michael1308/PogoProbe/assembly/20230415_011109.jpg

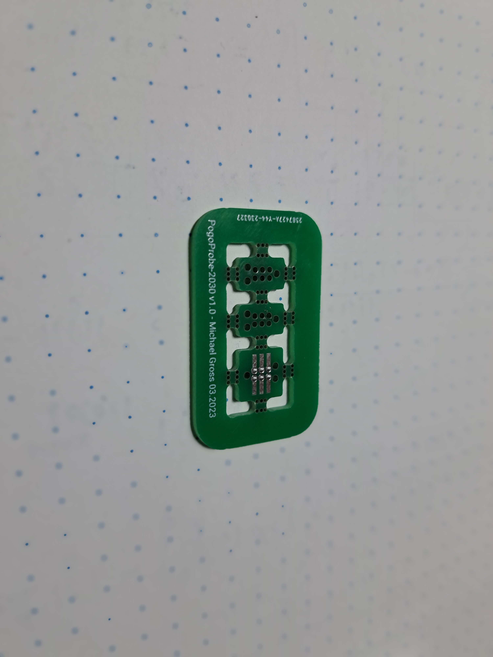
assembly/20230415_011109.jpg
