michael1308/PogoProbe/assembly/20230415_012053.jpg

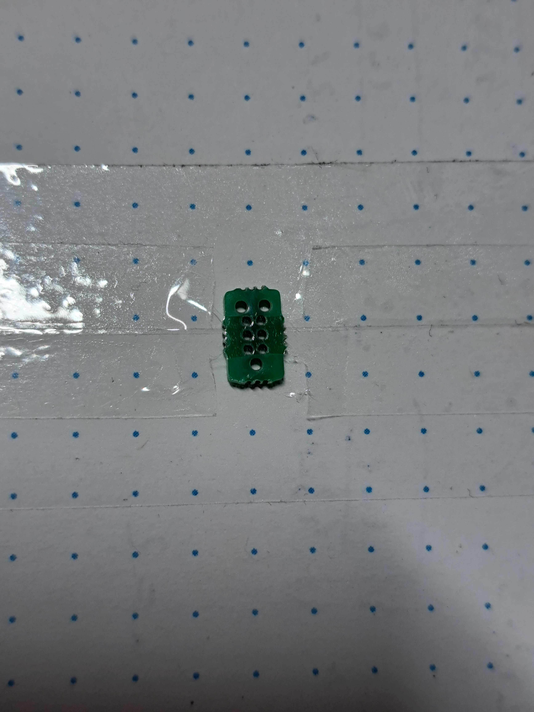
assembly/20230415_012053.jpg
