michael1308/PogoProbe/assembly/20230415_012128.jpg

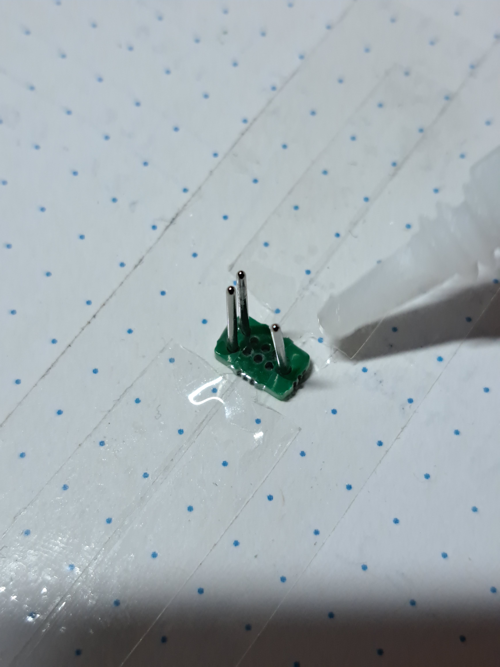
assembly/20230415_012128.jpg
