michael1308/PogoProbe/assembly/20230415_012207.jpg

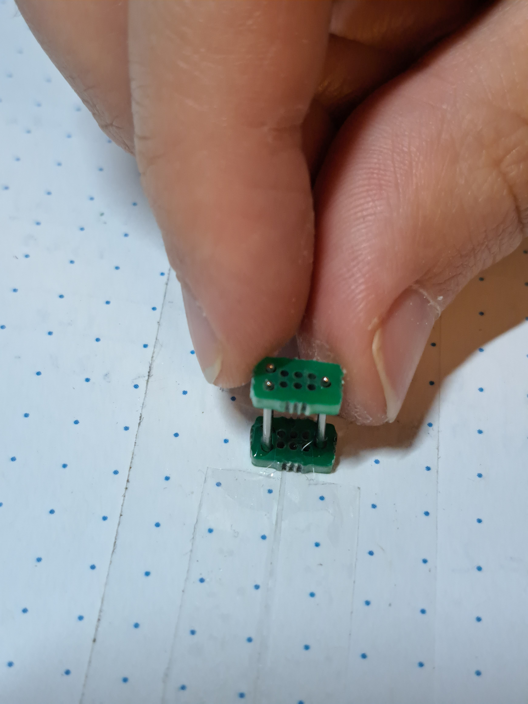
assembly/20230415_012207.jpg
