michael1308/PogoProbe/assembly/20230415_012923.jpg

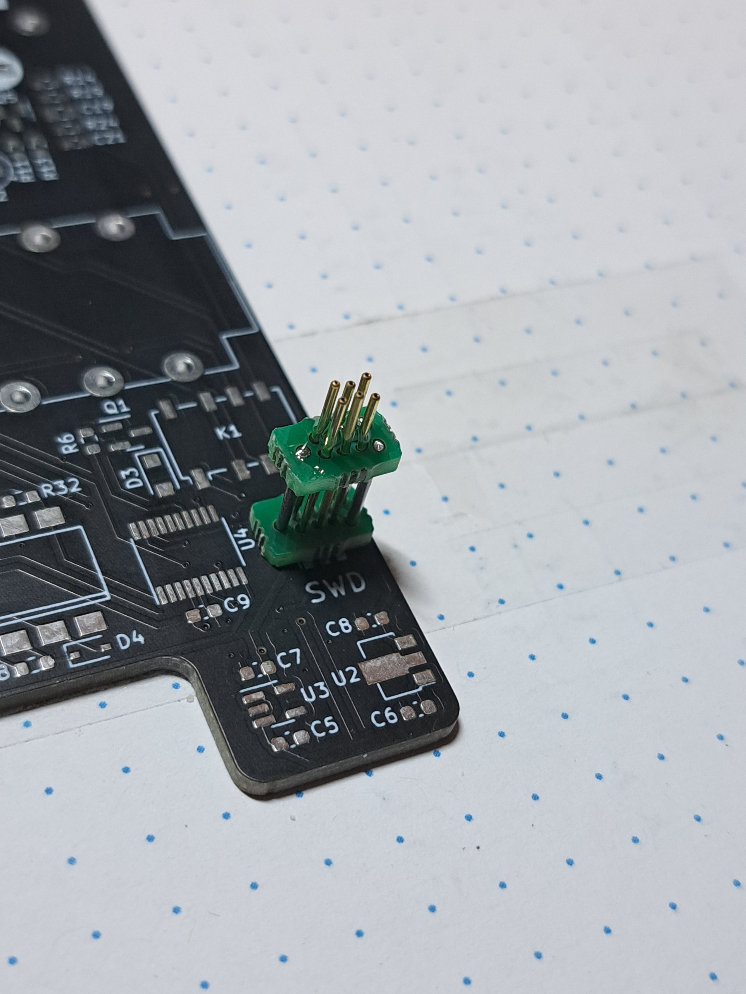
assembly/20230415_012923.jpg
