michael1308/PogoProbe/assembly/20230415_012853.jpg

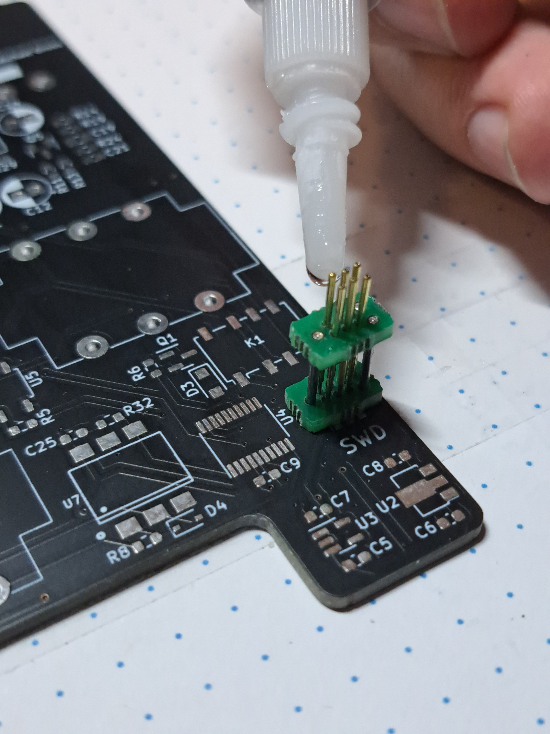
assembly/20230415_012853.jpg
